pdropes/Volumetric-Display/Arduino/Arduino V2.2.1 config.png

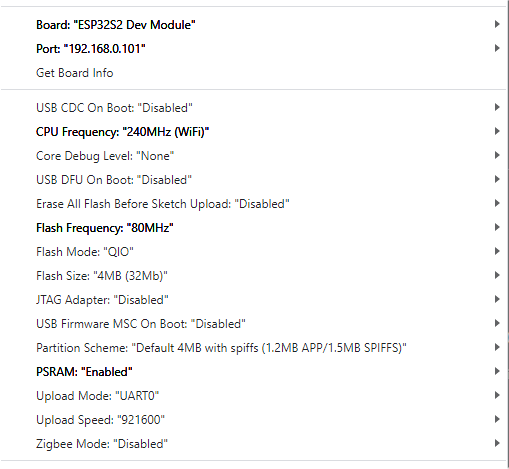
Arduino/Arduino V2.2.1 config.png
