pdropes/Volumetric-Display/Info/pcb-trace-width-vs-current-flow-1.gif

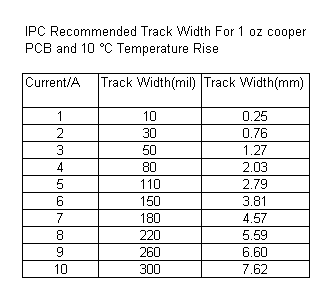
Info/pcb-trace-width-vs-current-flow-1.gif
