pdropes/Volumetric-Display/Info/pts636-3051079  - SMT F leads.png

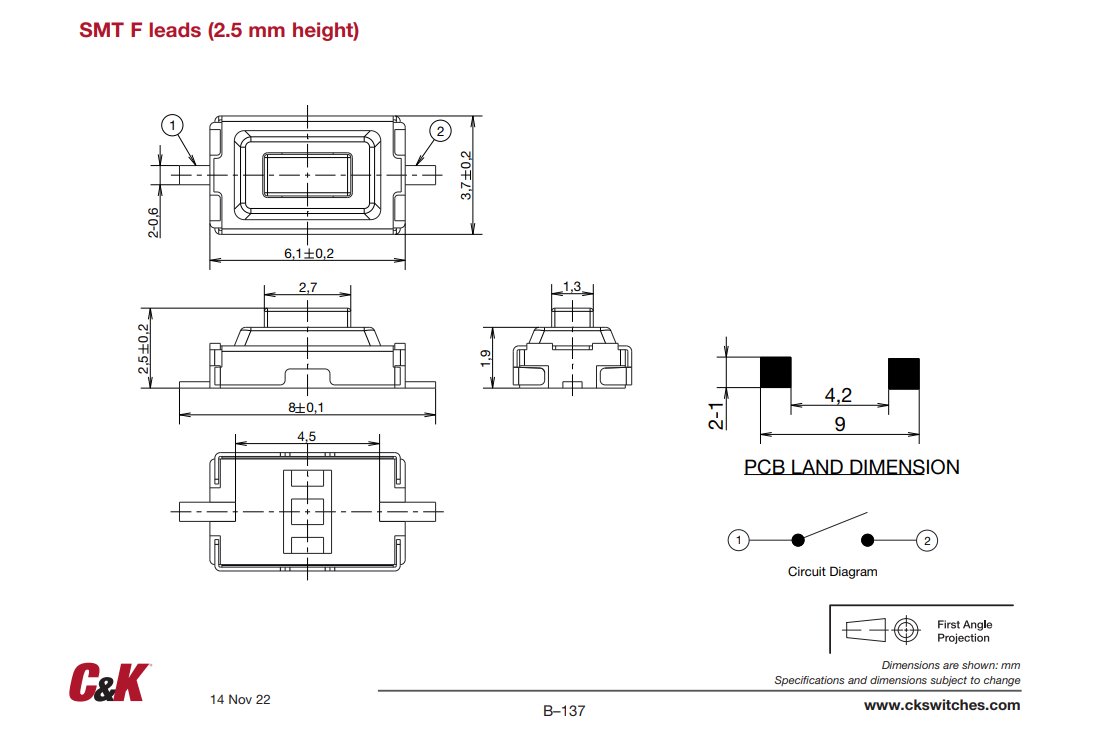
Info/pts636-3051079 - SMT F leads.png
