pdropes/Volumetric-Display/Info/tube.jpg

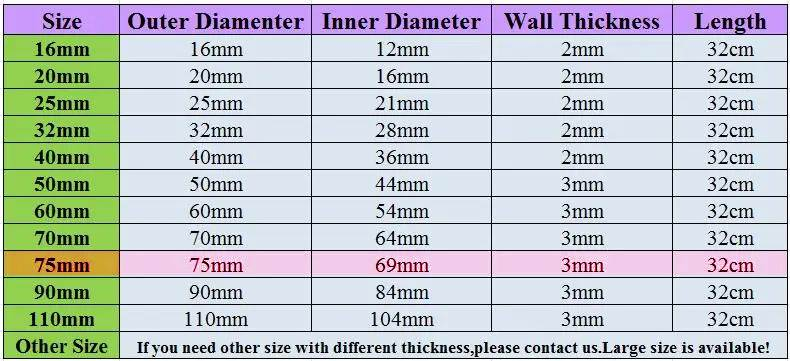
Info/tube.jpg
