pdropes/Volumetric-Display/Info/Wireless/ezgif-3-dbbc2a15a1.jpg

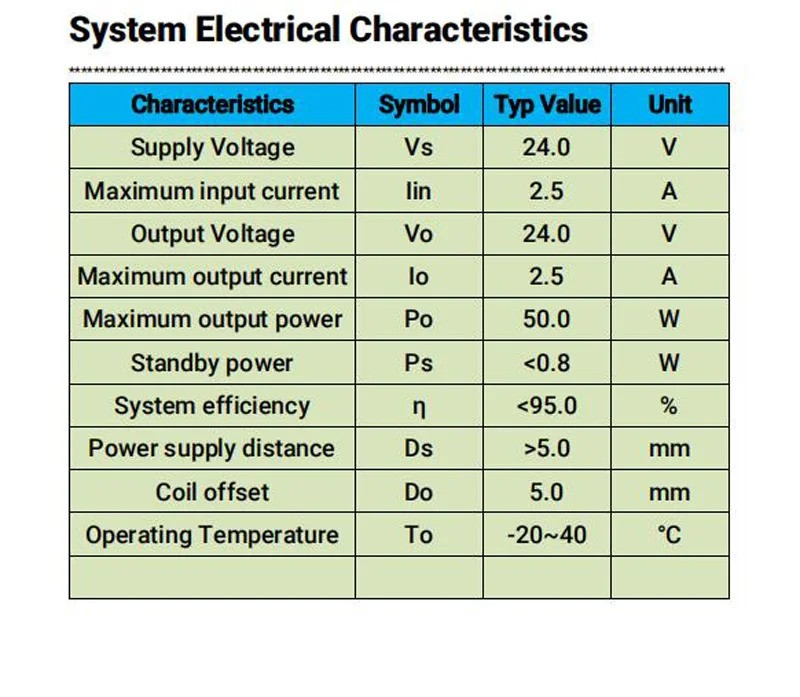
Info/Wireless/ezgif-3-dbbc2a15a1.jpg
