pdropes/Volumetric-Display/Info/Wireless/Receiver.jpg

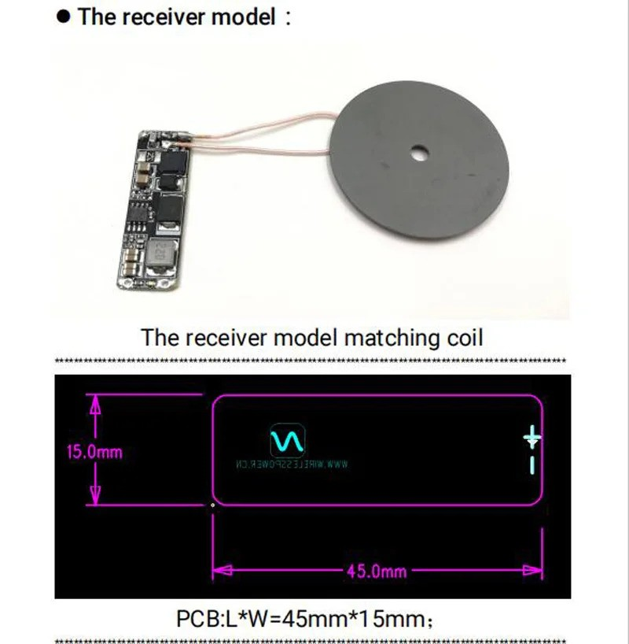
Info/Wireless/Receiver.jpg
