pdropes/Volumetric-Display/Photos/POV_01.png

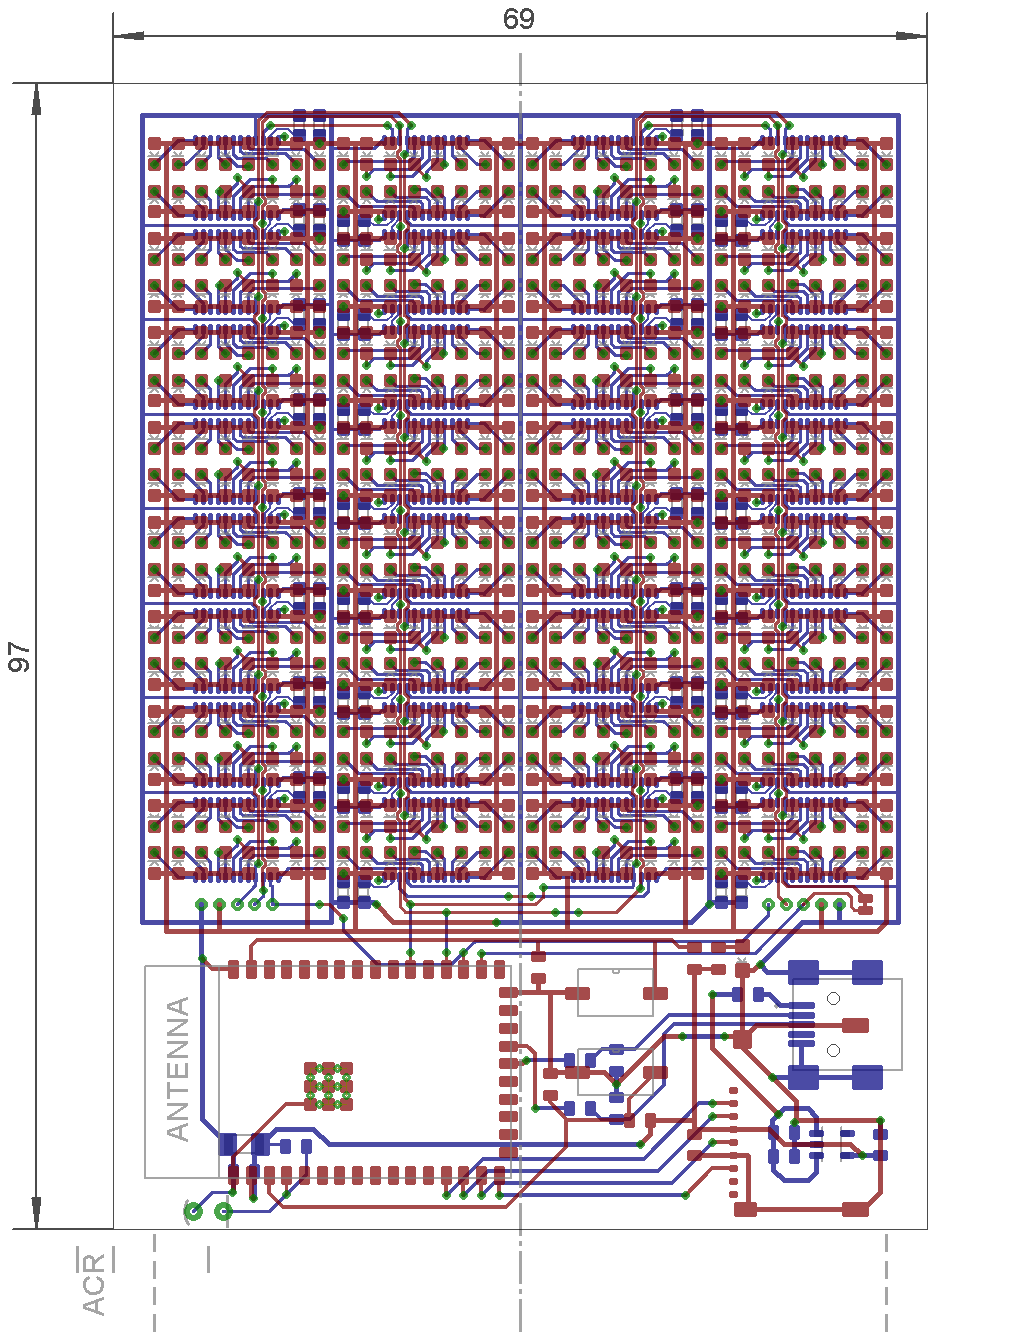
Photos/POV_01.png
