pdropes/Volumetric-Display/Photos/POV_02.png

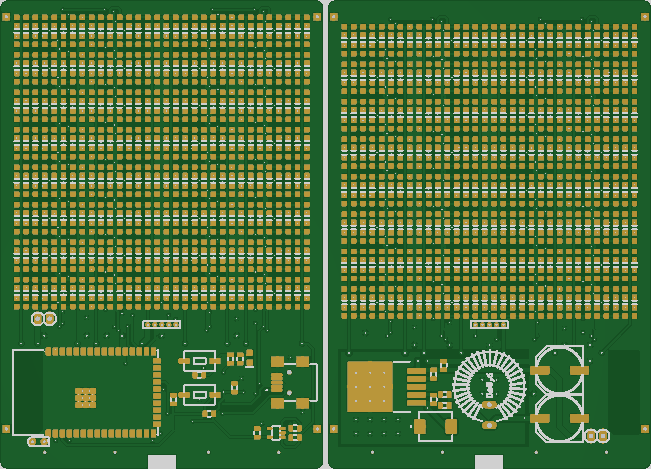
Photos/POV_02.png
