pdropes/Volumetric-Display/Photos/POV_03.png

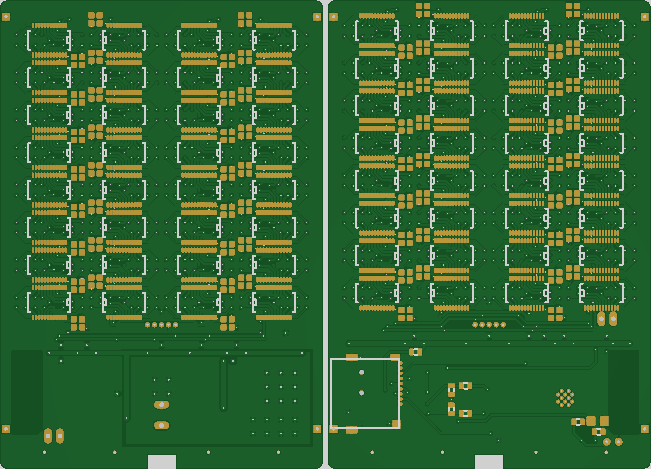
Photos/POV_03.png
