pdropes/Volumetric-Display/Photos/POV_04.jpg

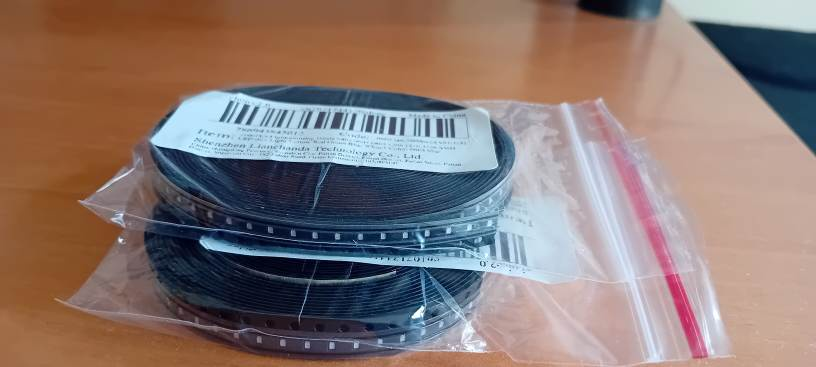
Photos/POV_04.jpg
