pdropes/Volumetric-Display/Photos/POV_05.jpg

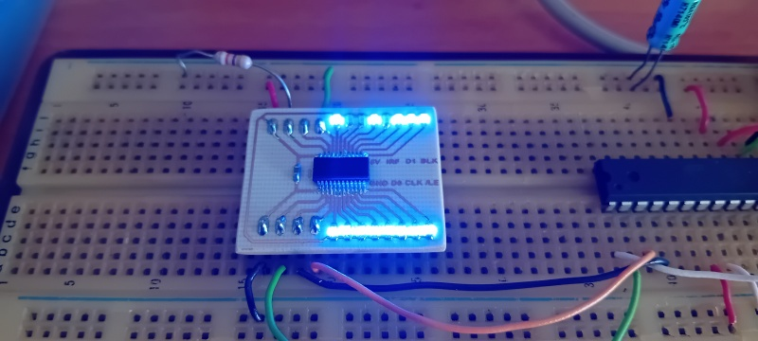
Photos/POV_05.jpg
