pdropes/Volumetric-Display/Photos/POV_08.jpg

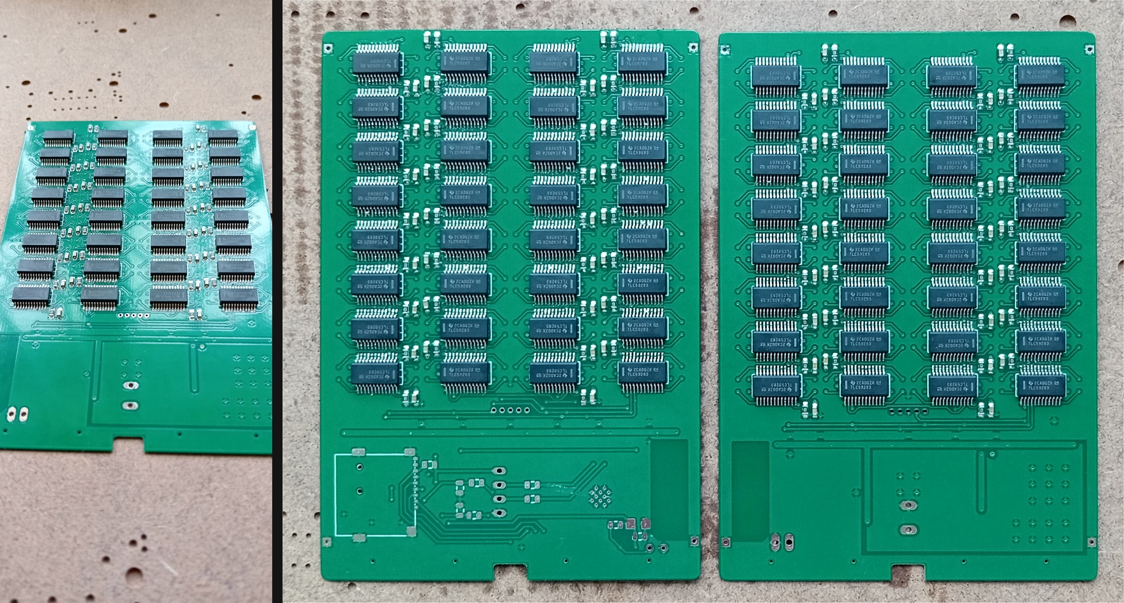
Photos/POV_08.jpg
