pdropes/Volumetric-Display/Photos/POV_09.jpg

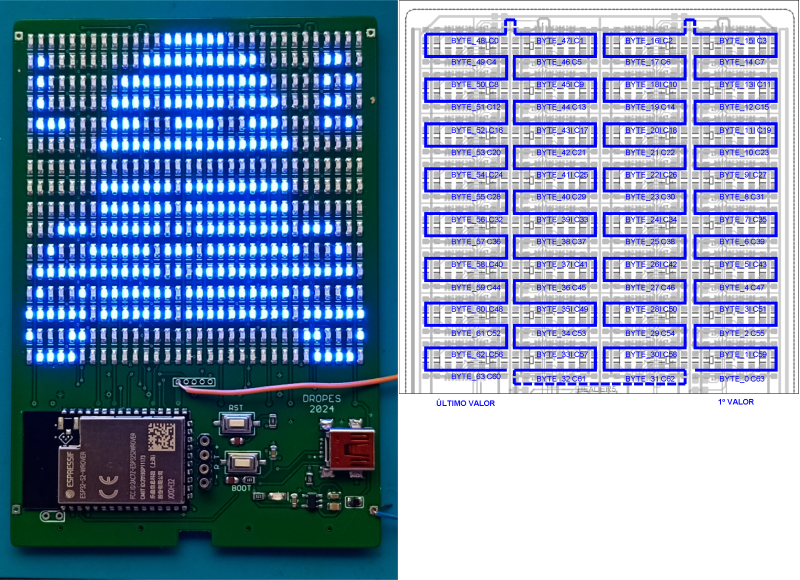
Photos/POV_09.jpg
