pdropes/Volumetric-Display/Photos/POV_10.jpg

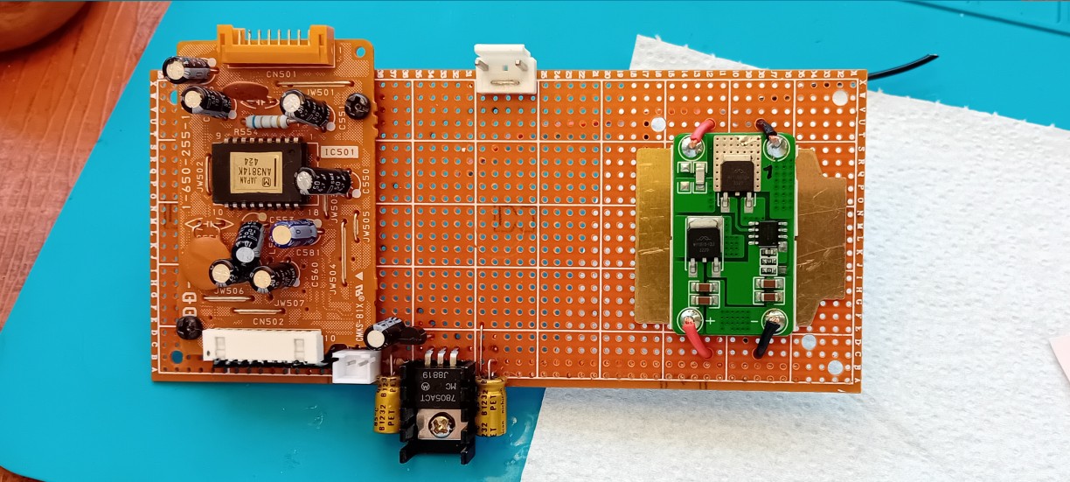
Photos/POV_10.jpg
