pdropes/Volumetric-Display/Photos/POV_11.jpg

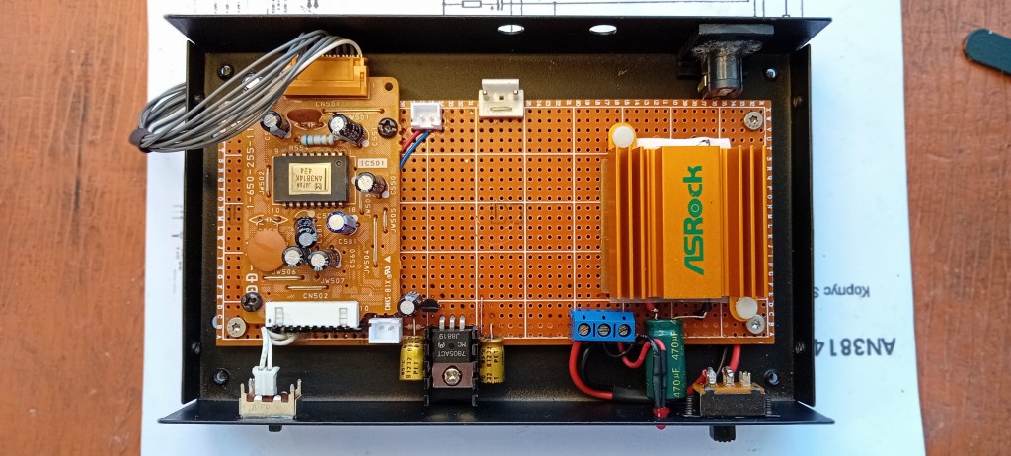
Photos/POV_11.jpg
