pdropes/Volumetric-Display/Photos/POV_13.jpg

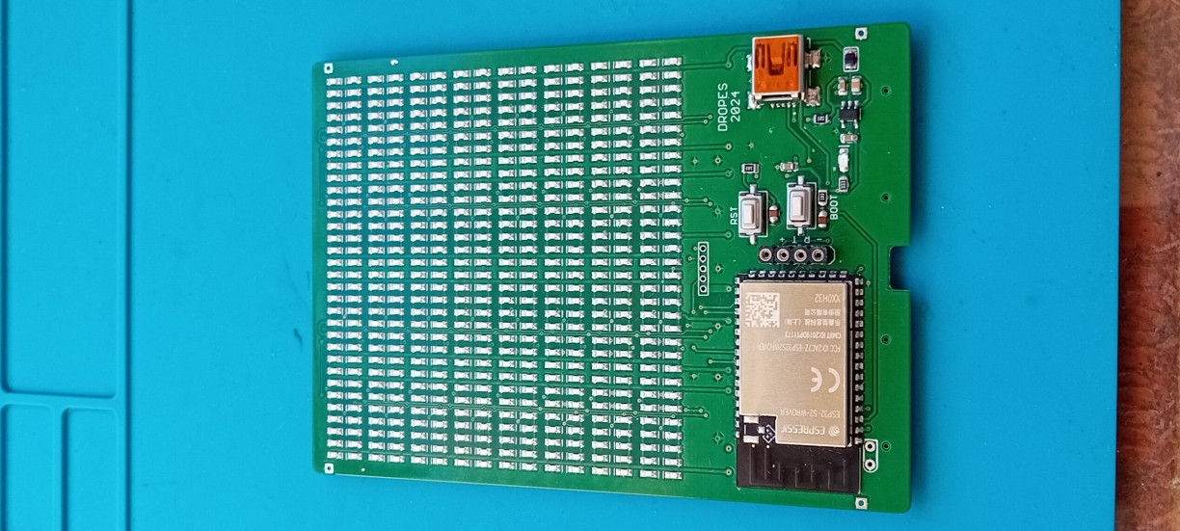
Photos/POV_13.jpg
