pdropes/Volumetric-Display/Photos/POV_14.jpg

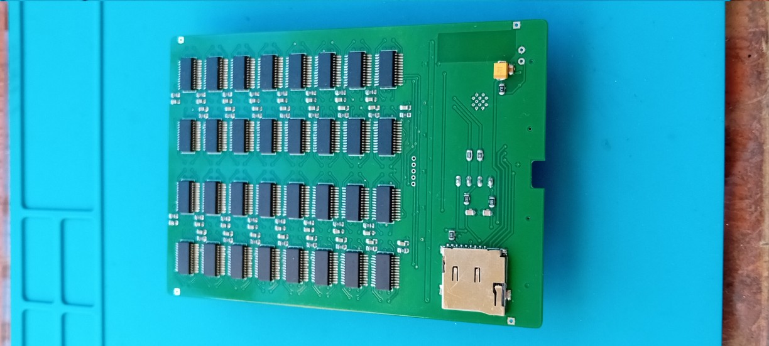
Photos/POV_14.jpg
