pdropes/Volumetric-Display/Photos/POV_15.jpg

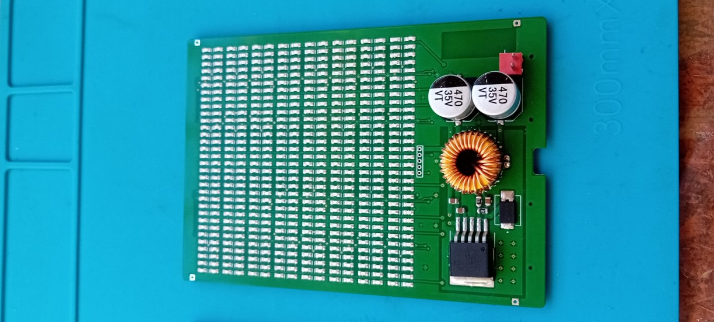
Photos/POV_15.jpg
