pdropes/Volumetric-Display/Photos/POV_16.jpg

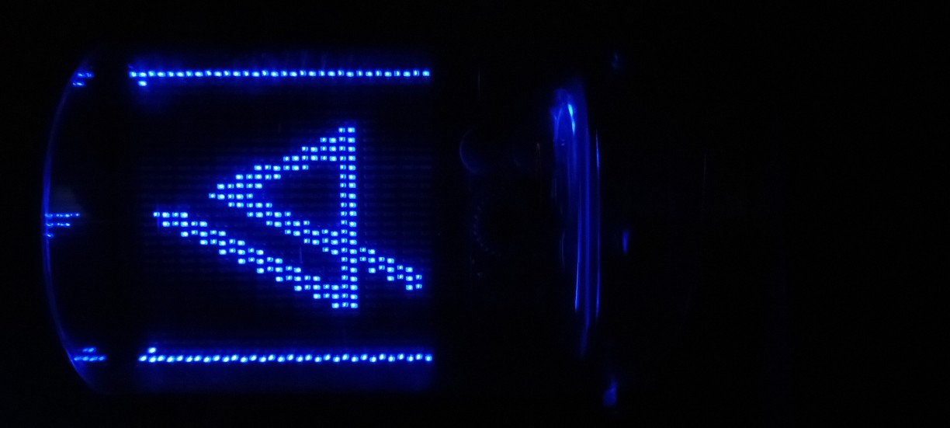
Photos/POV_16.jpg
