pdropes/Volumetric-Display/Photos/POV_18.jpg

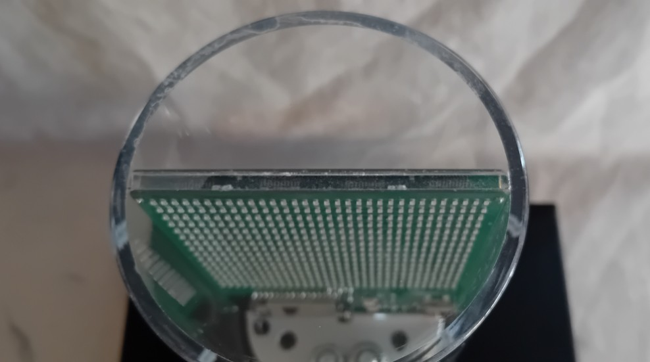
Photos/POV_18.jpg
