pdropes/Volumetric-Display/Info/Serial order_board1.png

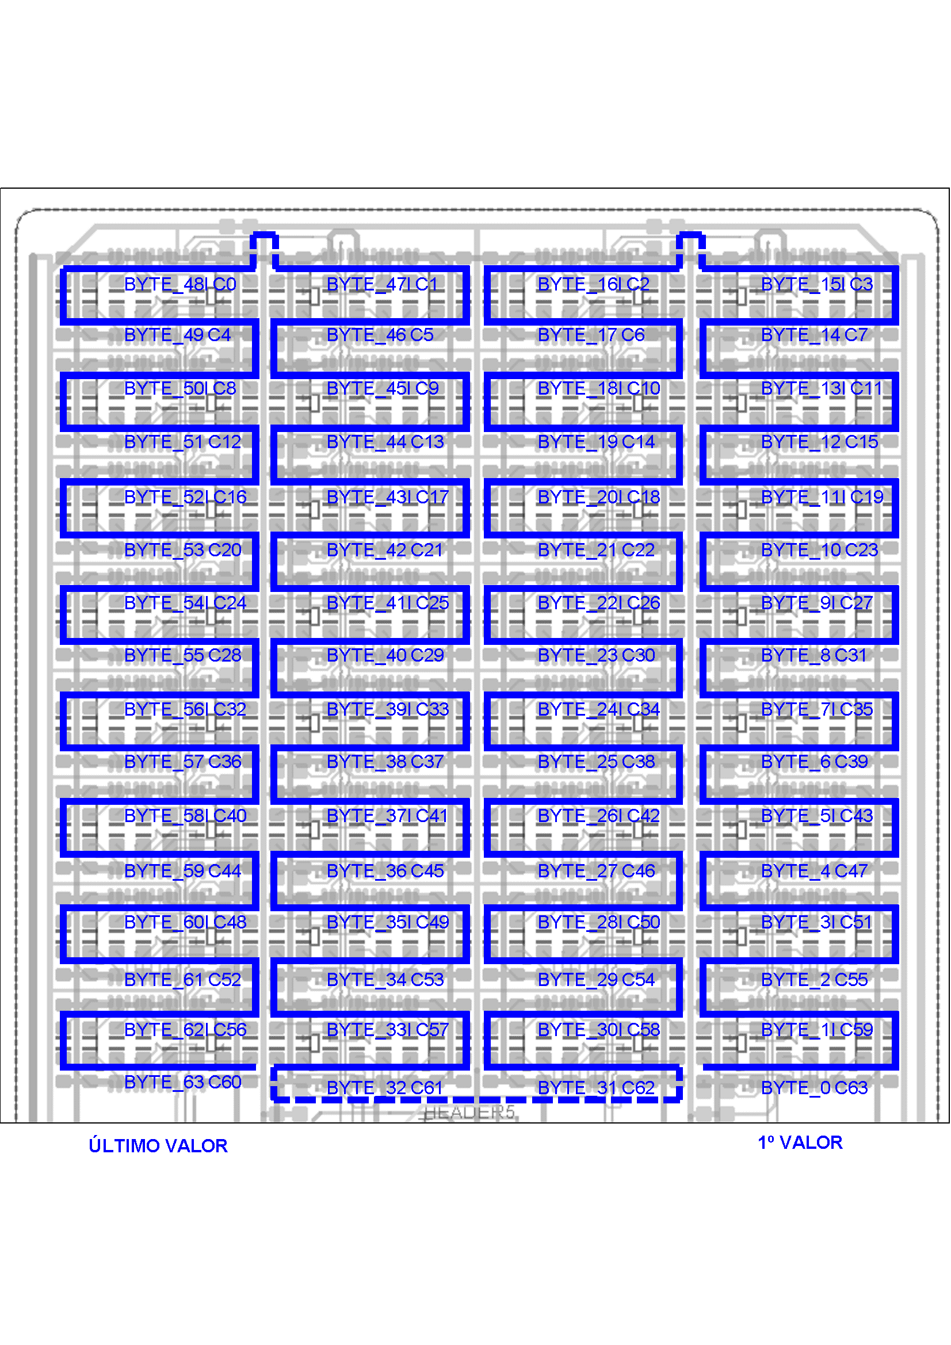
Info/Serial order_board1.png
